tfranks31/Budget-Handheld-Raman-Spectrometer/Src/HRS/src/modules/Relay.cpp

#include <Arduino.h>
#include <modules/Relay.hpp>

Relay::Relay(uint8_t pinNum)
{
    this->pinNum = pinNum;
}

void Relay::init()
{
    pinMode(pinNum, OUTPUT);
    turnOff();
}

void Relay::turnOn()
{
    digitalWrite(pinNum, HIGH);
}

void Relay::turnOff()
{
    digitalWrite(pinNum, LOW);
}
